Cuprum77/LCD_Driver/src/ise/i2c_edid.v

/*
Copyright (c) 2015, Takeshi Matsuya <macchan@sfc.wide.ad.jp>
All rights reserved.

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
1. Redistributions of source code must retain the above copyright notice,
   this list of conditions and the following disclaimer. 
2. Redistributions in binary form must reproduce the above copyright notice,
   this list of conditions and the following disclaimer in the documentation
   and/or other materials provided with the distribution. 

THIS SOFTWARE IS PROVIDED BY THE COPYRIGHT HOLDERS AND CONTRIBUTORS "AS IS" AND
ANY EXPRESS OR IMPLIED WARRANTIES, INCLUDING, BUT NOT LIMITED TO, THE IMPLIED
WARRANTIES OF MERCHANTABILITY AND FITNESS FOR A PARTICULAR PURPOSE ARE
DISCLAIMED. IN NO EVENT SHALL THE COPYRIGHT OWNER OR CONTRIBUTORS BE LIABLE FOR
ANY DIRECT, INDIRECT, INCIDENTAL, SPECIAL, EXEMPLARY, OR CONSEQUENTIAL DAMAGES
(INCLUDING, BUT NOT LIMITED TO, PROCUREMENT OF SUBSTITUTE GOODS OR SERVICES;
LOSS OF USE, DATA, OR PROFITS; OR BUSINESS INTERRUPTION) HOWEVER CAUSED AND
ON ANY THEORY OF LIABILITY, WHETHER IN CONTRACT, STRICT LIABILITY, OR TORT
(INCLUDING NEGLIGENCE OR OTHERWISE) ARISING IN ANY WAY OUT OF THE USE OF THIS
SOFTWARE, EVEN IF ADVISED OF THE POSSIBILITY OF SUCH DAMAGE.

The views and conclusions contained in the software and documentation are those
of the authors and should not be interpreted as representing official policies, 
either expressed or implied, of the FreeBSD Project.
*/
`default_nettype none
// `include "../../../boards/atlys/rtl/setup.v"

module i2c_edid
#(
//	parameter HEX_FILE = "/home/tmatsuya/i2c_edid/software/edid/DELL3007WFP.hex"
	parameter HEX_FILE = "/home/tmatsuya/i2c_edid/software/edid/HP2159.hex"
) (
`ifdef DEBUG
	input wire [7:0] switch,
	output wire [7:0] led,
`endif
	input wire clk,
	input wire rst,
	input wire scl,
	inout wire sda
);

reg         hiz = 1'b1;
reg         sda_out = 1'b0;
reg [4:0]   count = 5'd0;
reg [15:0]  rdata = 24'h0;
reg [7:0]   addr = 8'h0;
reg [7:0]   data = 8'h0;
parameter   EDID_IDLE     = 3'b000;
parameter   EDID_ADDR     = 3'b001;
parameter   EDID_ADDR_ACK = 3'b010;
parameter   EDID_ADDR_ACK2= 3'b011;
parameter   EDID_DATA     = 3'b100;
parameter   EDID_DATA_ACK = 3'b101;
parameter   EDID_DATA_ACK2= 3'b110;
reg [2:0]   edid_state = EDID_IDLE;
reg [3:0]   scl_data = 4'h00;
reg [3:0]   sda_data = 4'h00;
`ifdef DEBUG
reg [7:0]   led_r [0:255];
reg [7:0]   led_count = 8'h00;
`endif

wire        scl_posedge, scl_negedge, scl_high;
assign scl_posedge = (scl_data == 4'b0111);
assign scl_negedge = (scl_data == 4'b1000);
assign scl_high    = (scl_data == 4'b1111);

wire [7:0] dout;
edid_rom # (
	.HEX_FILE(HEX_FILE)
) edid_rom_0 (
	.clk(clk),
	.addr(addr[7:0]),
	.dout(dout)
);


always @(posedge clk) begin
	if (rst) begin
		hiz <= 1'b1;
		sda_out <= 1'b0;
		count <= 5'd0;
		rdata <= 24'h0;
		addr <= 8'h0;
		data <= 8'h0;
		scl_data <= 4'h00;
		sda_data <= 4'h00;
	end else begin
		scl_data <= {scl_data[2:0], scl};
		sda_data <= {sda_data[2:0], sda};

		if (sda_data == 4'b1000 && scl_high) begin		// Start
			count <= 5'd0;
			hiz <= 1'b1;
			sda_out <= 1'b0;
			edid_state <= EDID_ADDR;
		end else if (sda_data == 4'b0111 && scl_high) begin	// Stop
			edid_state <= EDID_IDLE;
		end else
		case (edid_state)
		EDID_IDLE: begin
			hiz <= 1'b1;
			sda_out <= 1'b0;
		end
		EDID_ADDR: begin
			if (scl_posedge) begin
				count <= count + 5'd1;
				rdata  <= {rdata[14:0], sda};
				if (count[2:0] == 3'd7) begin
`ifdef DEBUG
if (led_count != 8'd255)
led_count <= led_count + 8'd1;
led_r[ led_count ] <= {rdata[6:0], sda};
`endif
					if (count == 5'd15)
						addr <= {rdata[6:0],sda};
					edid_state <= EDID_ADDR_ACK;
				end
			end
		end
		EDID_ADDR_ACK: begin
			if (scl_negedge) begin
				hiz <= 1'b0;
				sda_out <= 1'b0;
				if (count == 5'd8 && rdata [0] == 1'b1) begin
					data <= dout;
					edid_state <= EDID_DATA;
				end else begin
					edid_state <= EDID_ADDR_ACK2;
				end
			end
		end
		EDID_ADDR_ACK2: begin
			if (scl_negedge) begin
				hiz <= 1'b1;
				edid_state <= EDID_ADDR;
			end
		end
		EDID_DATA: begin
			if (scl_negedge) begin
				count <= count + 5'd1;
				hiz <= 1'b0;
				sda_out <= data[7];
				data <= {data[6:0], 1'b0};
				if (count[2:0] == 3'd7) begin
`ifdef 	DEBUG
if (led_count != 8'd255)
led_count <= led_count + 8'd1;
led_r[ led_count ] <= dout;
`endif
					addr <= addr + 8'h1;
					edid_state <= EDID_DATA_ACK;
				end
			end
		end
		EDID_DATA_ACK: begin
			if (scl_negedge) begin
				data <= dout;
				hiz <= 1'b1;
				sda_out <= 1'b0;
				edid_state <= EDID_DATA_ACK2;
			end
		end
		EDID_DATA_ACK2: begin
			if (scl_posedge) begin
				if (sda)
					edid_state <= EDID_IDLE;
				else
					edid_state <= EDID_DATA;
			end
		end
		endcase
	end
end

assign sda = hiz ? 1'hz : sda_out;
`ifdef DEBUG
assign led = led_r[switch];
`endif

endmodule // edid

module edid_rom #(
	parameter ADDR_WIDTH = 8,
	parameter DATA_WIDTH = 8,
	parameter HEX_FILE = "/home/tmatsuya/i2c_edid/software/edid/DELL3007WFP.hex"
) (
	input  wire                  clk,
	input  wire [ADDR_WIDTH-1:0] addr,
	output wire [DATA_WIDTH-1:0] dout
);

reg [DATA_WIDTH-1:0] rom [0:2**ADDR_WIDTH-1];
reg [ADDR_WIDTH-1:0] q_addr;

initial begin
	$readmemh(HEX_FILE, rom, 0, 2**ADDR_WIDTH-1);
end

always @(posedge clk) begin
	q_addr <= addr;
end

assign dout = rom[q_addr];

endmodule // edid_rom
`default_nettype wire
